andilge/Futai-Encoder-WS2811-ring/dimensions/2-boards-in-blank-cover-panel.jpg

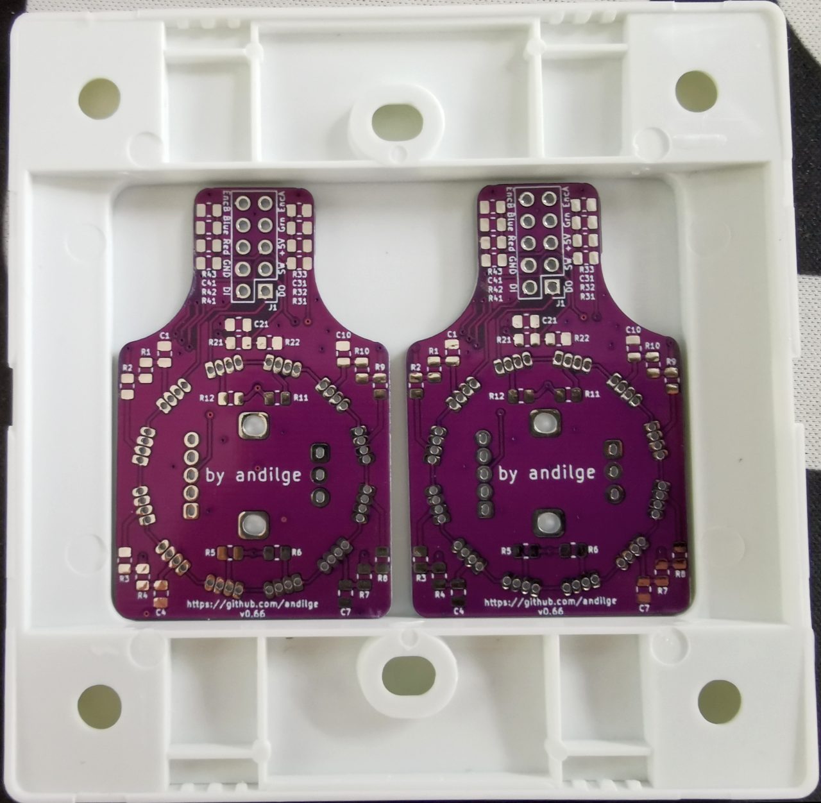
dimensions/2-boards-in-blank-cover-panel.jpg
