andilge/Futai-Encoder-WS2811-ring/dimensions/encoder-center-to-edge-y.png

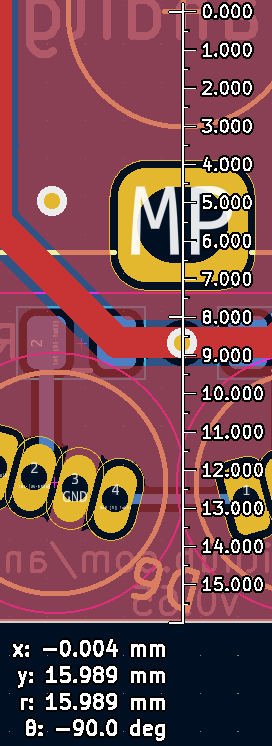
dimensions/encoder-center-to-edge-y.png
