andilge/Futai-Encoder-WS2811-ring/dimensions/x-edge-2-edge.png

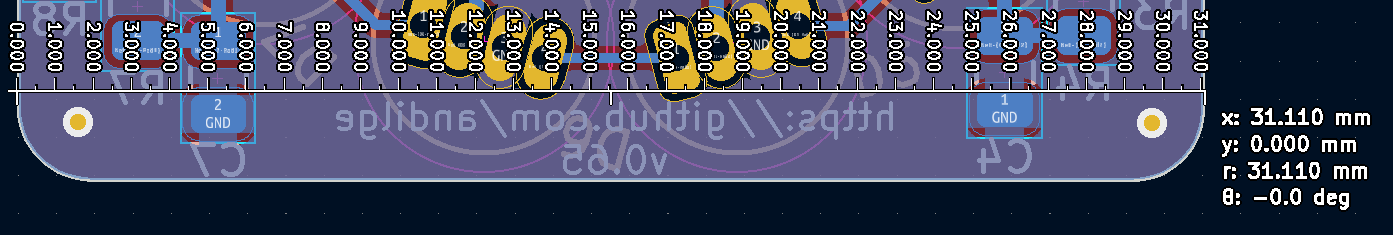
dimensions/x-edge-2-edge.png
