andilge/Futai-Encoder-WS2811-ring/images/building-it-up.jpg

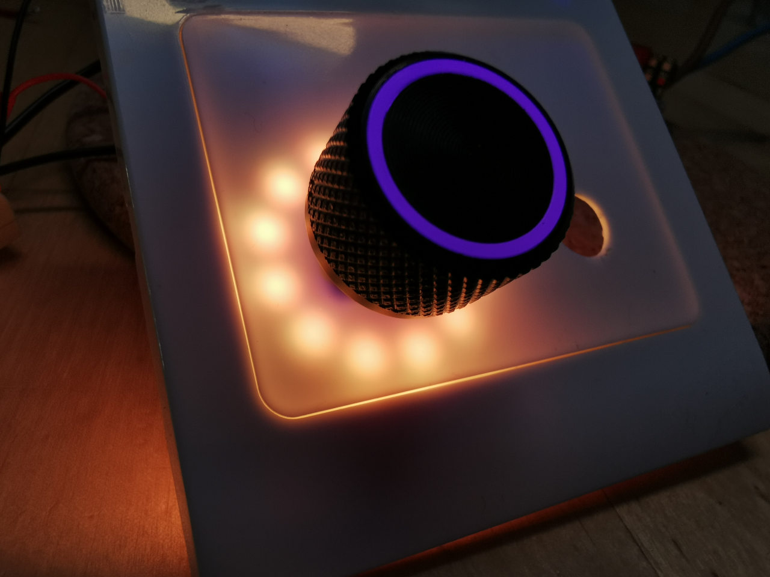
images/building-it-up.jpg
